turetax/td5-carplay-gauge/cad/reference_thingiverse_5856588/Binacle_Front_Plate_v1.1_Thicker_Bezle.stl

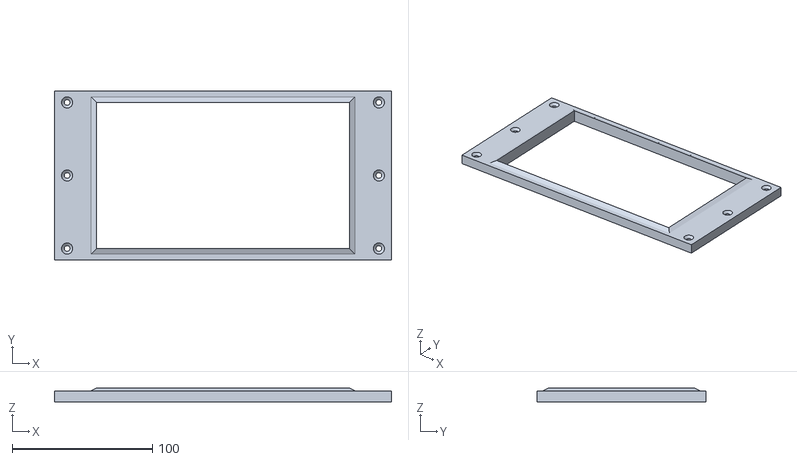
[picture p15: CAD file, 2026-09-05]
cad/reference_thingiverse_5856588/Binacle_Front_Plate_v1.1_Thicker_Bezle.stl
240.0 x 120.0 x 10.0
