turetax/td5-carplay-gauge/cad/stl/defender_mount_slot_template.stl

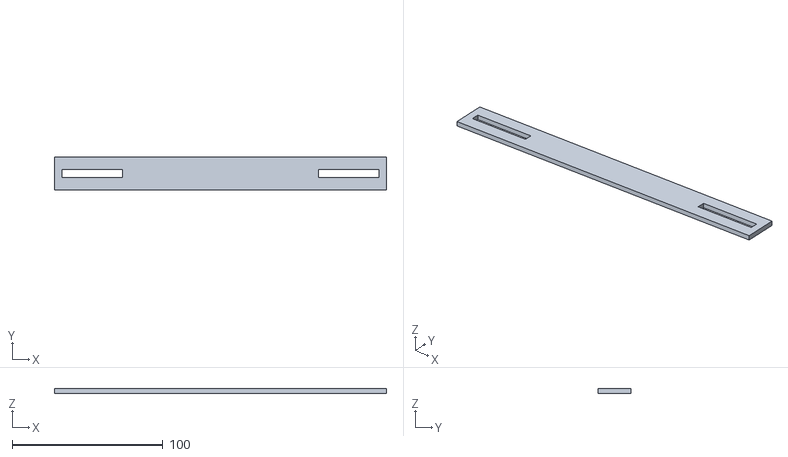
[picture p16: CAD file, 2026-09-05]
cad/stl/defender_mount_slot_template.stl
220.0 x 22.0 x 3.00
