turetax/td5-carplay-gauge/3d print/Defender_EP0189_V21_plus5mm_helt_fri_skarmvolym_V38.stl

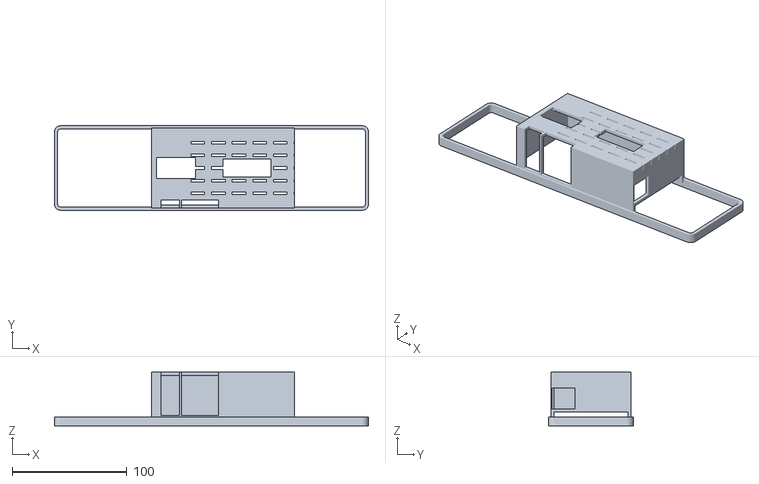
[picture p17: CAD file, 2026-09-14]
3d print/Defender_EP0189_V21_plus5mm_helt_fri_skarmvolym_V38.stl
273.8 x 73.8 x 46.8
