turetax/td5-carplay-gauge/3d print/Defender_EP0189_V21_plus5mm_bada_gavlar_fri_skarmyta_V31.stl

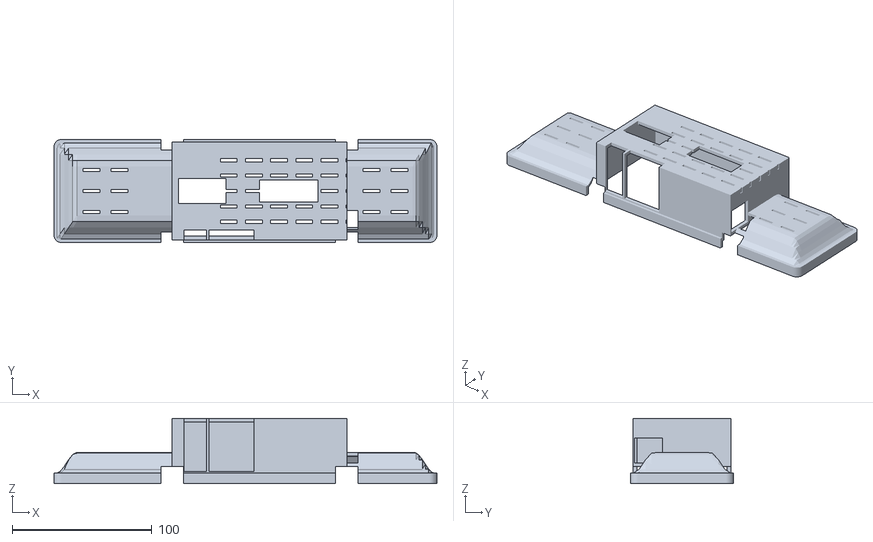
[picture p18: CAD file, 2026-09-14]
3d print/Defender_EP0189_V21_plus5mm_bada_gavlar_fri_skarmyta_V31.stl
273.8 x 73.8 x 46.8
