turetax/td5-carplay-gauge/3d print/Defender_EP0189_V37_fast_90grad_M4_V42.stl

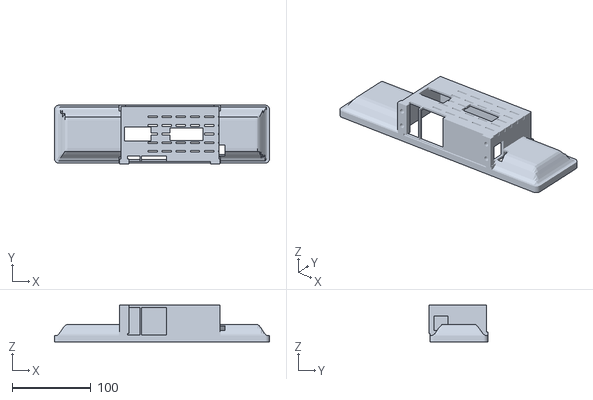
[picture p19: CAD file, 2026-09-14]
3d print/Defender_EP0189_V37_fast_90grad_M4_V42.stl
273.8 x 75.0 x 46.8
