turetax/td5-carplay-gauge/3d print/Defender_EP0189_V22_form_plus5mm_oppet_front_V24.stl

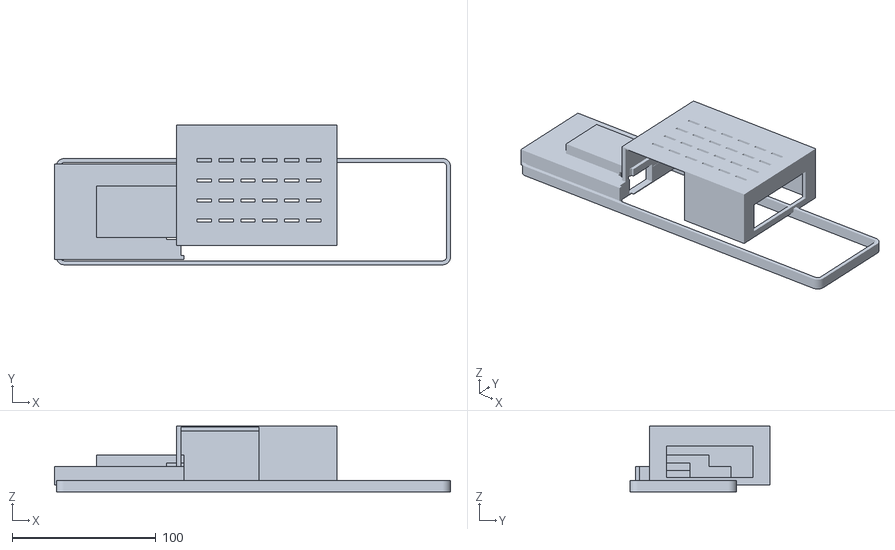
[picture p20: CAD file, 2026-09-14]
3d print/Defender_EP0189_V22_form_plus5mm_oppet_front_V24.stl
275.0 x 97.0 x 45.8
