turetax/td5-carplay-gauge/3d print/Defender_EP0189_V21_plus5mm_fri_skarmyta_usb_gavel_V30.stl

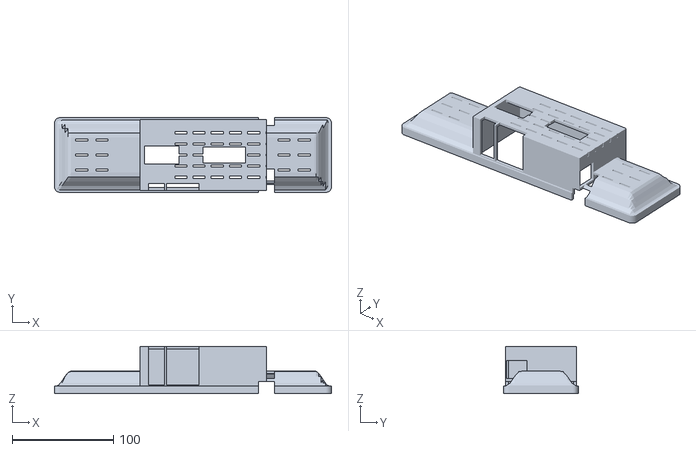
[picture p23: CAD file, 2026-09-14]
3d print/Defender_EP0189_V21_plus5mm_fri_skarmyta_usb_gavel_V30.stl
273.8 x 73.8 x 46.8
