turetax/td5-carplay-gauge/3d print/Defender_EP0189_V37_fast90_vanster_gavel_hoger_aterstalld_V48.stl

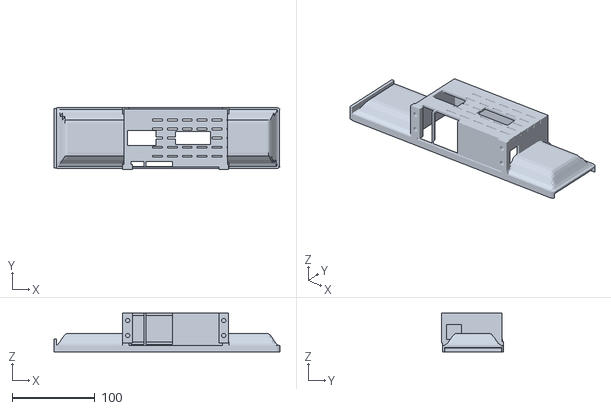
[picture p24: CAD file, 2026-09-14]
3d print/Defender_EP0189_V37_fast90_vanster_gavel_hoger_aterstalld_V48.stl
272.8 x 75.0 x 46.8
