turetax/td5-carplay-gauge/3d print/Defender_EP0189_slutna_konvexa_bakstycken_fri_skarmvolym_V51.stl

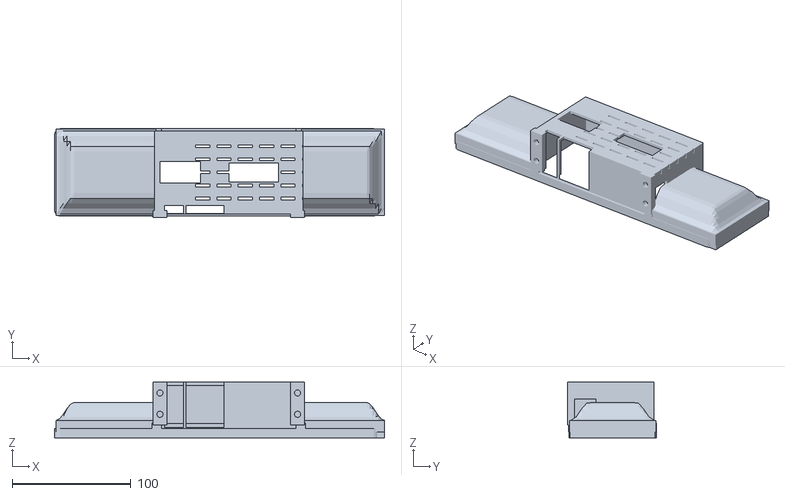
[picture p25: CAD file, 2026-09-14]
3d print/Defender_EP0189_slutna_konvexa_bakstycken_fri_skarmvolym_V51.stl
278.2 x 75.0 x 46.8
