turetax/td5-carplay-gauge/3d print/Defender_EP0189_V21_plus5mm_pibox_utan_luft_V27.stl

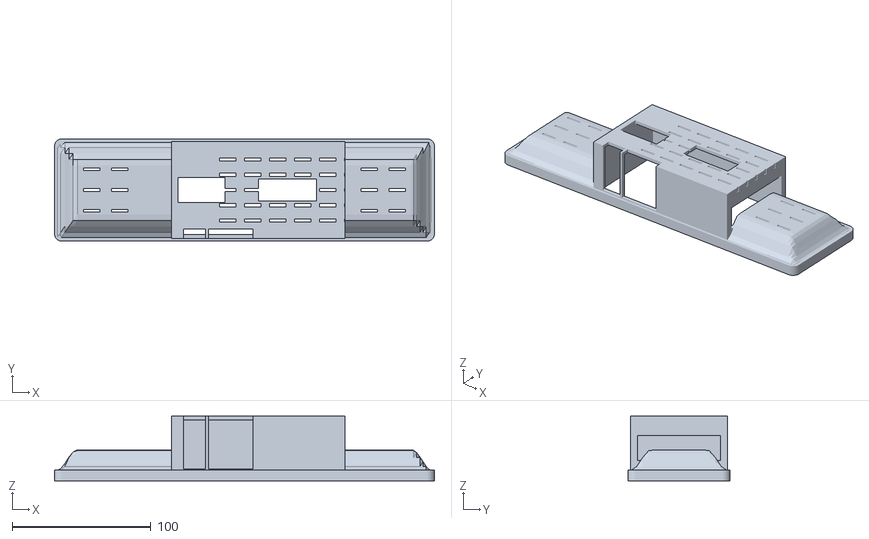
[picture p27: CAD file, 2026-09-14]
3d print/Defender_EP0189_V21_plus5mm_pibox_utan_luft_V27.stl
273.8 x 73.8 x 46.8
