turetax/td5-carplay-gauge/3d print/Defender_EP0189_V21_plus5mm_utan_markerade_delar_V28.stl

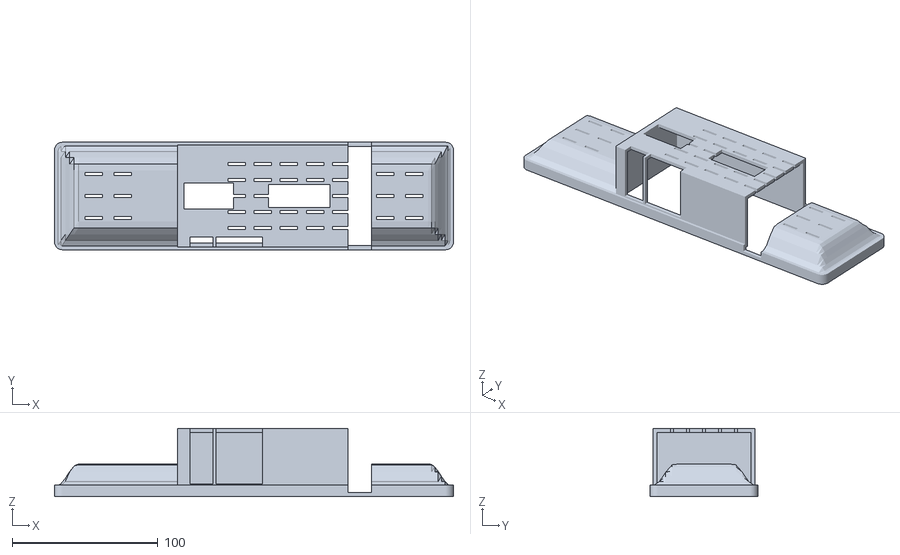
[picture p28: CAD file, 2026-09-14]
3d print/Defender_EP0189_V21_plus5mm_utan_markerade_delar_V28.stl
273.8 x 73.8 x 46.8
