turetax/td5-carplay-gauge/3d print/Defender_EP0189_konvex_fran_6mm_utan_mellankant_V53.stl

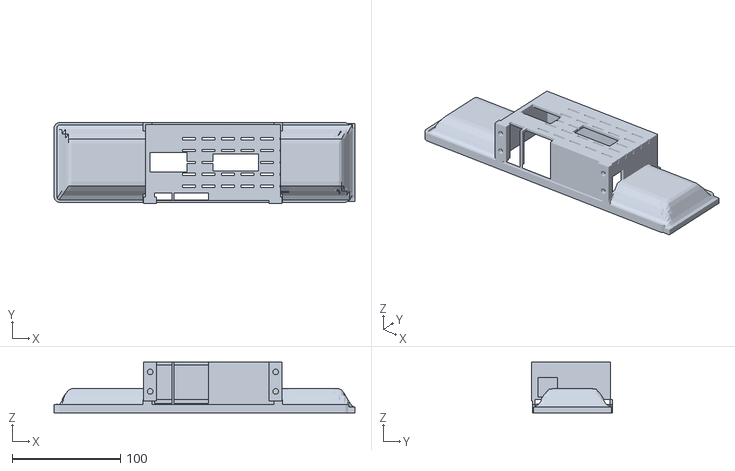
[picture p29: CAD file, 2026-09-14]
3d print/Defender_EP0189_konvex_fran_6mm_utan_mellankant_V53.stl
278.2 x 75.0 x 46.8
