turetax/td5-carplay-gauge/3d print/Defender_EP0189_mattad_baksida_utan_armar_V22.stl

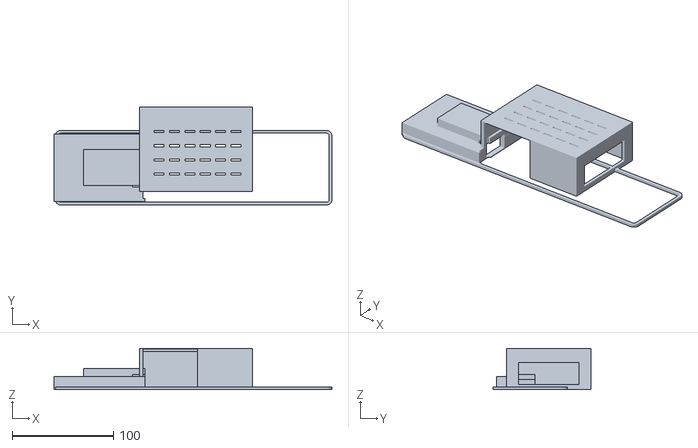
[picture p30: CAD file, 2026-09-14]
3d print/Defender_EP0189_mattad_baksida_utan_armar_V22.stl
275.0 x 97.0 x 40.8
