turetax/td5-carplay-gauge/3d print/Defender_EP0189_slutna_konvexa_bakstycken_originaldjup_V52.stl

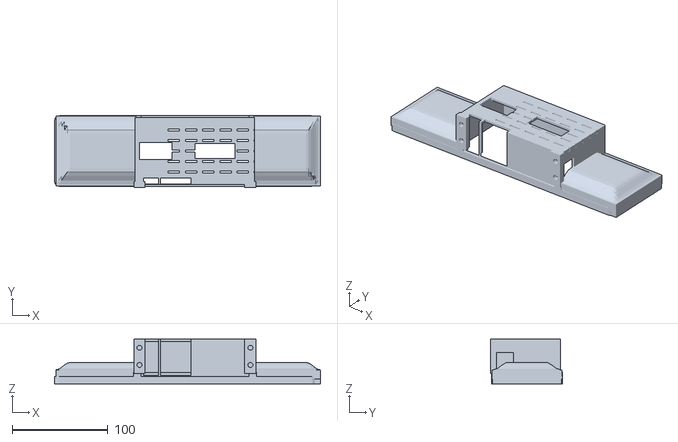
[picture p31: CAD file, 2026-09-14]
3d print/Defender_EP0189_slutna_konvexa_bakstycken_originaldjup_V52.stl
278.2 x 75.0 x 46.8
