turetax/td5-carplay-gauge/3d print/Defender_EP0189_V21_plus5mm_trianglar_bakom_skarm_V35.stl

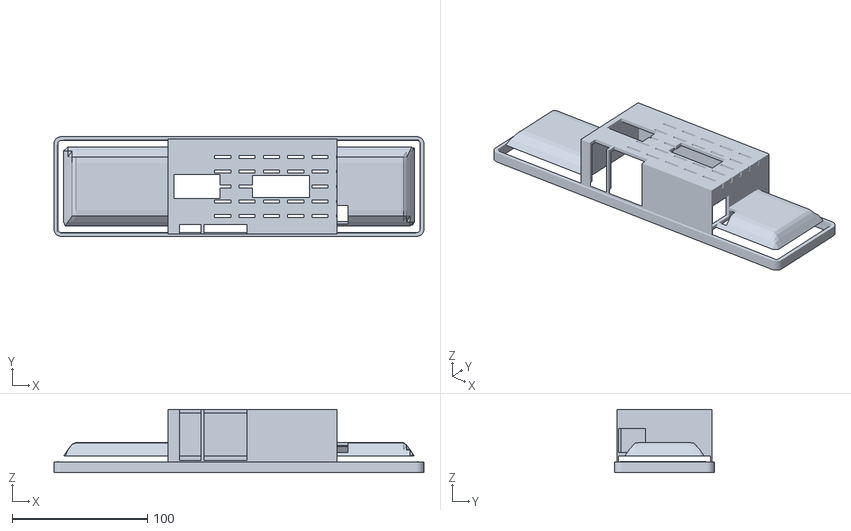
[picture p32: CAD file, 2026-09-14]
3d print/Defender_EP0189_V21_plus5mm_trianglar_bakom_skarm_V35.stl
273.8 x 73.8 x 46.8
