turetax/td5-carplay-gauge/3d print/Defender_EP0189_konvexa_gavlar_2mm_hogerspel_V50.stl

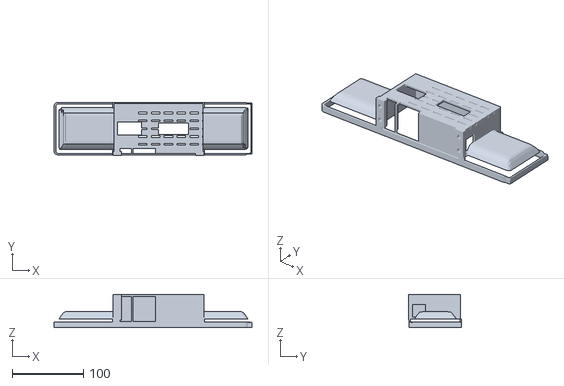
[picture p33: CAD file, 2026-09-14]
3d print/Defender_EP0189_konvexa_gavlar_2mm_hogerspel_V50.stl
278.2 x 75.0 x 46.8
