turetax/td5-carplay-gauge/3d print/Defender_relabox_lock_fast_skarm_90grad_V25.stl

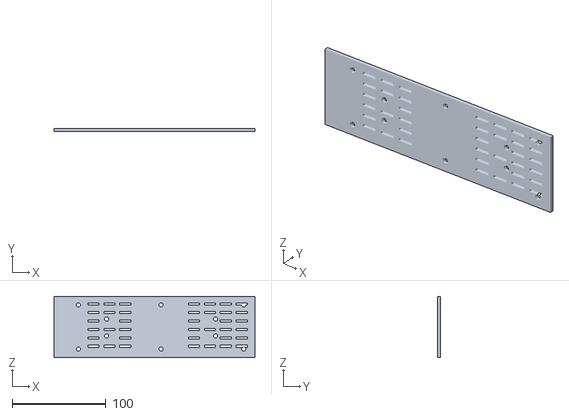
[picture p34: CAD file, 2026-09-14]
3d print/Defender_relabox_lock_fast_skarm_90grad_V25.stl
214.0 x 3.00 x 65.0
