turetax/td5-carplay-gauge/3d print/Defender_EP0189_frameless_symmetrisk_rak_V23.stl

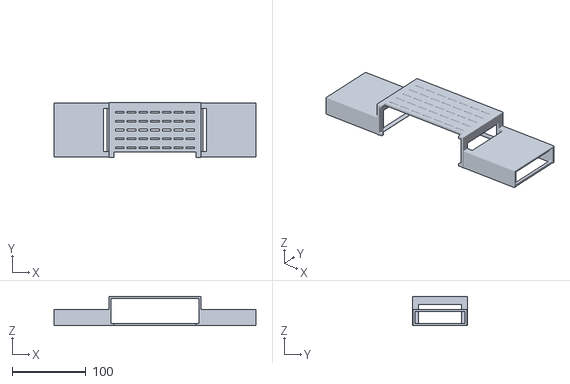
[picture p35: CAD file, 2026-09-14]
3d print/Defender_EP0189_frameless_symmetrisk_rak_V23.stl
274.8 x 75.0 x 39.8
