turetax/td5-carplay-gauge/3d print/Defender_relabox_rela_vanster_V15.stl

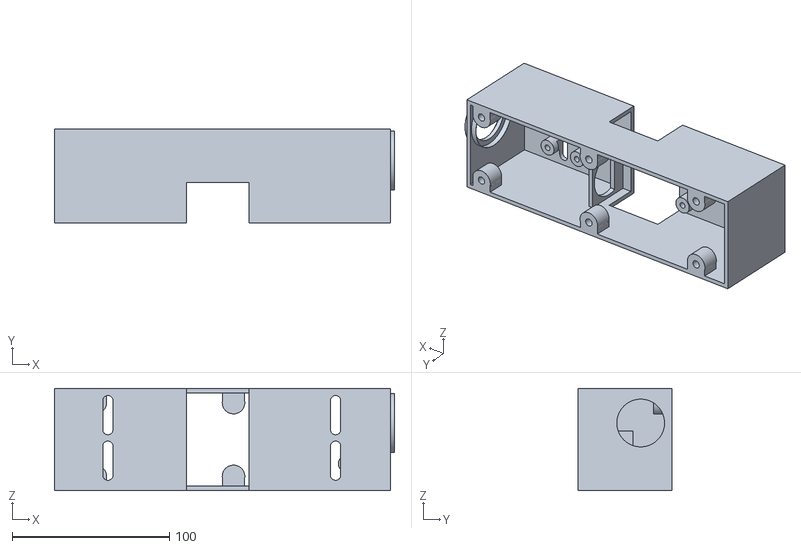
[picture p36: CAD file, 2026-09-05]
3d print/Defender_relabox_rela_vanster_V15.stl
216.5 x 60.0 x 65.0
