turetax/td5-carplay-gauge/3d print/Defender_EP0189_utan_armfasten_kabeloppningar_V21.stl

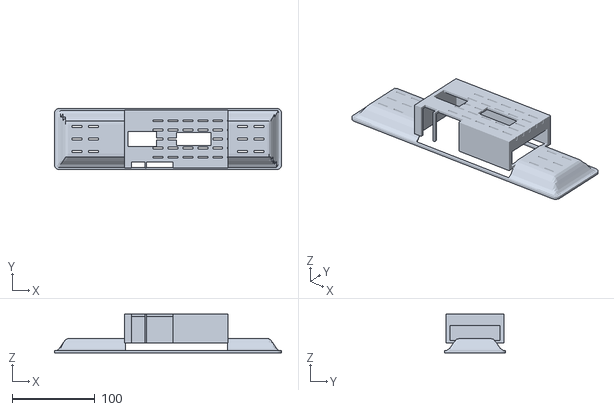
[picture p37: CAD file, 2026-09-05]
3d print/Defender_EP0189_utan_armfasten_kabeloppningar_V21.stl
273.8 x 73.8 x 46.8
